MaraGhe/InkTime/Images/exploded_view_2.png

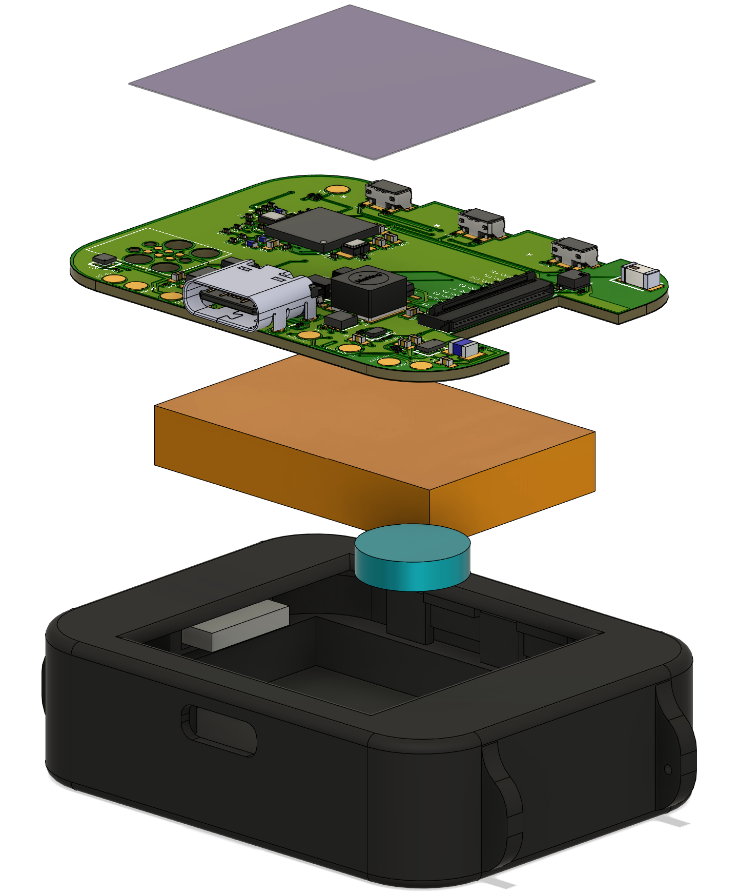
Images/exploded_view_2.png
