MaraGhe/InkTime/Images/normal_view.png

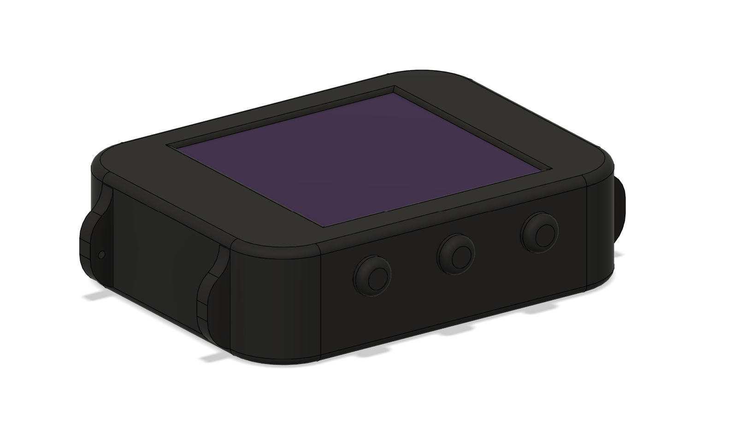
Images/normal_view.png
