MaraGhe/InkTime/Images/normal_view_interior.png

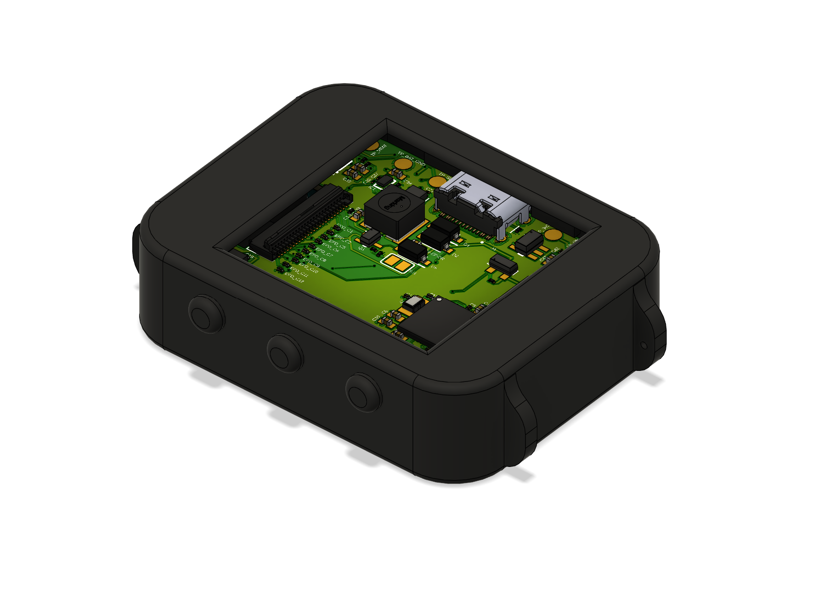
Images/normal_view_interior.png
