MaraGhe/InkTime/Images/normal_view_layered.png

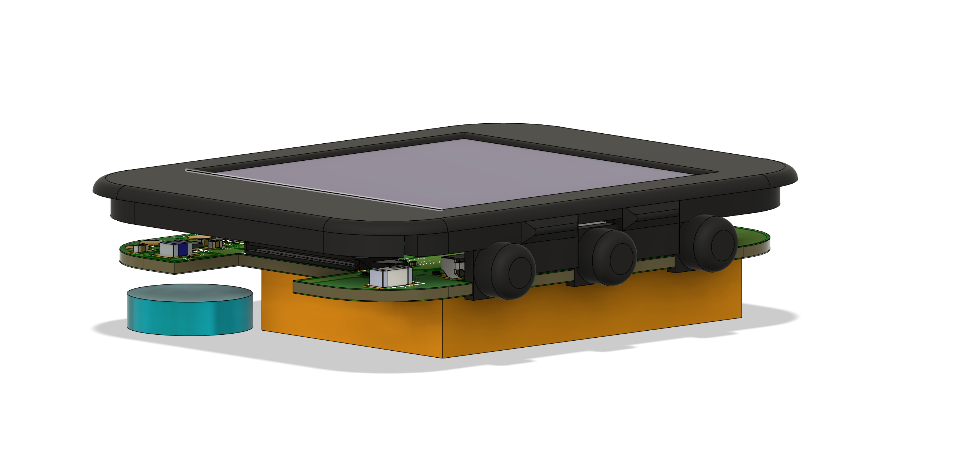
Images/normal_view_layered.png
