MaraGhe/InkTime/Images/exploded_view_all_components.png

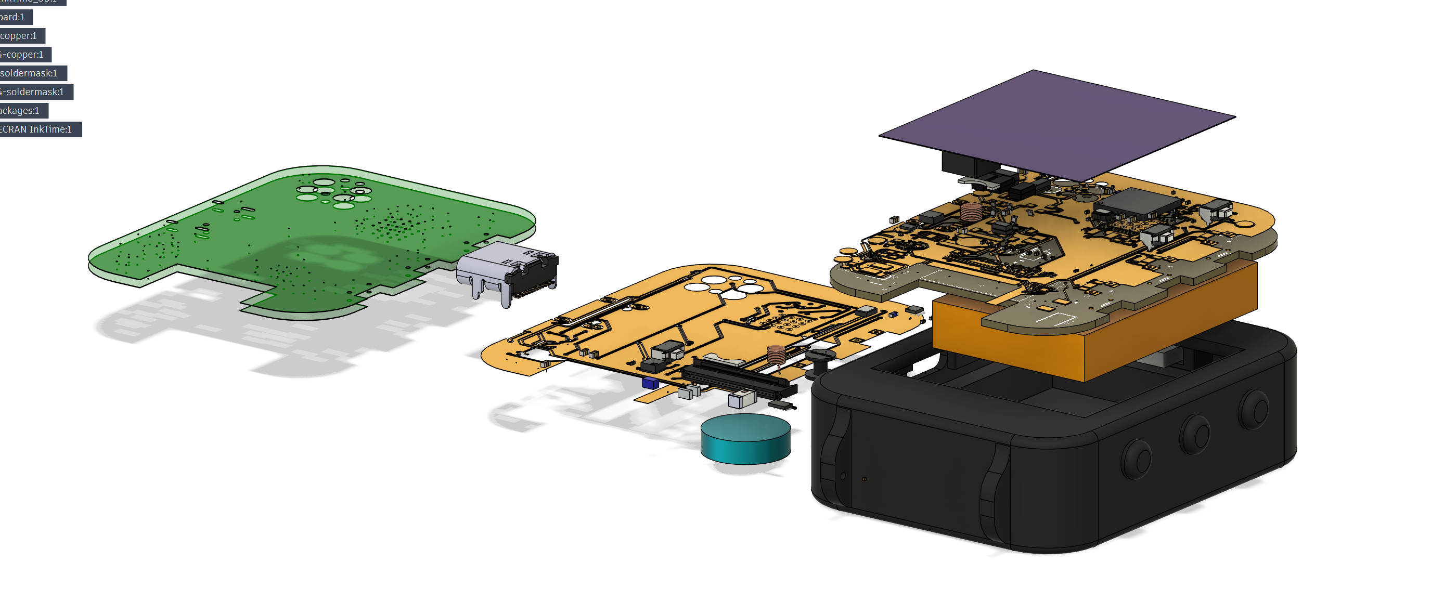
Images/exploded_view_all_components.png
